JochiSt/OpenFlowMeter/images/aisler/EEPROM_jumper.PNG

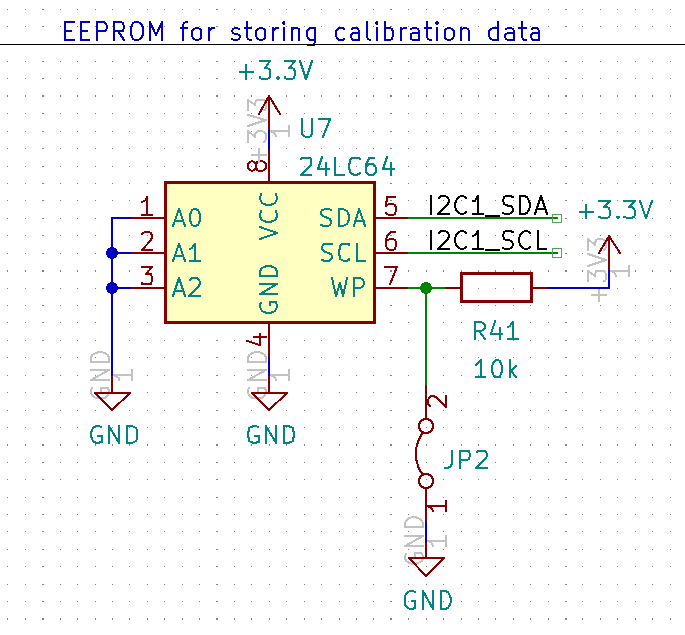
images/aisler/EEPROM_jumper.PNG
