JochiSt/OpenFlowMeter/simulations/CurrentSource/images/current_source_mod_v1_Iout_vs_Uin.PNG

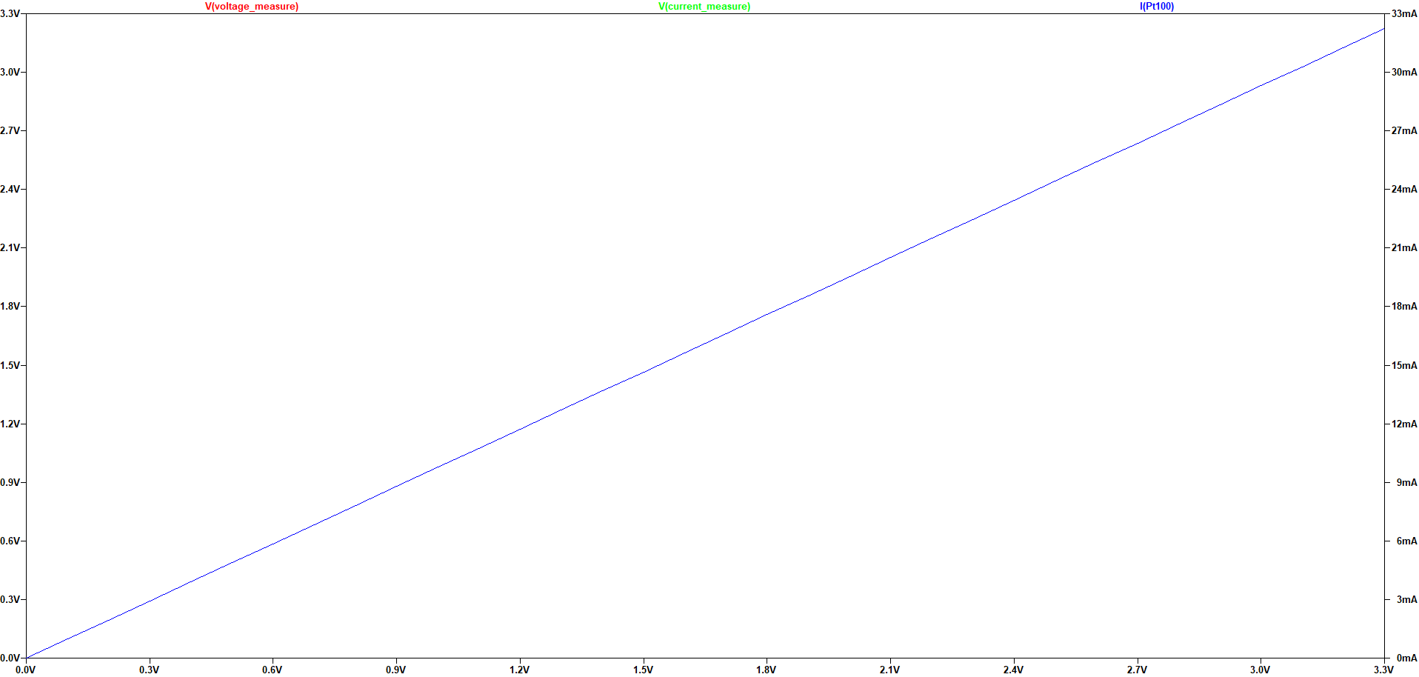
simulations/CurrentSource/images/current_source_mod_v1_Iout_vs_Uin.PNG
