JochiSt/OpenFlowMeter/software/measurements/3V3_zener_voltage_current.png

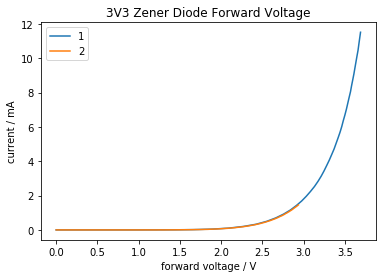
software/measurements/3V3_zener_voltage_current.png
