JochiSt/OpenFlowMeter/software/testing/calibration_20220307_190727_CH0_100.png

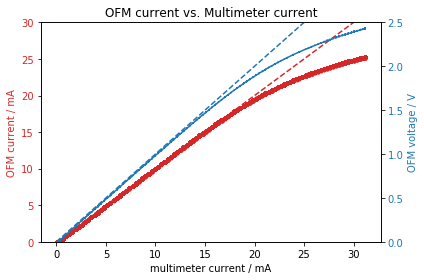
software/testing/calibration_20220307_190727_CH0_100.png
