JochiSt/OpenFlowMeter/simulations/AmplifierBias/SwitchableGainAmplifier.asc

C1: cap; 100n
R1: res; 47k
R2: res; 5k6
R5: res; 10k
R6: res; 100
U2: cd4066
U3: LT1491
V1: voltage; PULSE(0 3.3 1 10p 10p 1 2)
V2: voltage; PULSE(0 3.3 1 1 10p 0 1)
V3: voltage; 3.3
V4: voltage; PWL(0 0 2 0 2.1 0.5 4 0.5 4.1 1 6 1 6.1 1.5 8 1.5 8.1 2 10 2 10.1 2.5 12 2.5 12.1 3.3 14 3.3)
Named nets: 0, +3V3, AMPout, GainSwitch, AMPin, Vbias
.tran 14
