JochiSt/OpenFlowMeter/simulations/CurrentSource/current_source_mod_v1.asc

PT100: res; {R_PT100}
Q2: pnp; BC857C
R1: res; 47
R2: res; 100k
R3: res; 47k
R4: res; 47k
R5: res; 100
R6: res; 1k
R7: res; 220
R8: res; 22k
R9: res; 22k
R10: res; 10k
R11: res; 10k
R12: res; 10k
R13: res; 10k
R14: res; 10k
R15: res; 10k
R16: res; 8
R17: res; 8
R18: res; 8
R19: res; 8
U1: LT1490A
U2: LT1490A
U3: LT1490A
V1: voltage; 24
V3: voltage; 1.5
Named nets: +24V, 0, current_measure, voltage_measure, current_setpoint
.dc V3 0 3.3 0.1
.param R_PT100 100
R2 and R4 define current per input voltage
max. 3.3V
"protection" resistor
differential amplifier
measure voltage across R7
PT100 temperature sensor
.tran 1
.save V(voltage_measure) V(current_measure) I(Pt100)
.step param R_PT100 100 150 10
.measure Vmeas_avg avg V(voltage_measure)
.measure Imeas_avg avg V(current_measure)
.measure Ipt100_avg avg I(Pt100)
Simulate current vs PT100
Simulate current vs input voltage
