JochiSt/OpenFlowMeter/simulations/PWMFilter/pwm_filter_v1.asc

C1: cap; 100n
C2: cap; 100n
R1: res; {RR1}
R2: res; {RR2}
U1: LT1490A
V1: voltage; PULSE(0 3.3 0 1n 1n {Ton} {Tperiod}); AC 1
V2: voltage; 3.3
V3: voltage; {PWMoutVoltage}
Named nets: 0, 3V3, PWMin, Uout, OUTset
.param Ton={DutyCycle / FPWM}
.param Tperiod={ 1 / FPWM }
;.tran 0 20ms 0
* calculate PWM frequency
* MasterClock Frequency = 54MHz
.param FCLK={54Meg}
* ARR = 16bit = 65536
;.param ARR = {65536}
* ARR = 10bit = 1024
* ARR = 12bit = 4096
.param ARR = {4096}
* Prescaler
.param PSC ={0}
 * calculate PWM frequency
.param FPWM = {FCLK / ( (ARR + 1) * (PSC + 1) )}
 * calculate DutyCycle
.param DutyCycle = { CCR / ARR }
* relative PWM value
.param relPWM=0.3
* calculate timer setting
.param CCR = { ARR * relPWM }
* analog equivalent voltage
.param PWMoutVoltage = {3.3 * relPWM}
PWM setting
STM32 internal calculations
* See SPICE Error Log for result
.meas tran T1 find time when V(pwmin)=0 rise 1
.meas tran T2 find time when V(pwmin)=0 rise 2
.meas tran  Frequency param 1/(T2-T1)
.meas Cfreq PARAM FPWM
PWM output generation
Measure Frequency
.ac dec 100 10 1k
.meas gmax max(mag(V(uout)))
.meas AC f FIND frequency when mag(V(uout))=gmax/sqrt(2)
Measure -3B point (see log)
.step param RR2 list 1k 4k7 10k
.step param RR1 list 1k 4k7 10k
