JochiSt/OpenFlowMeter/simulations/GainSwitchAmplifier/SwitchableGainAmplifier.asc

C1: cap; 100n
M1: nmos; BSS123
R1: res; 10k
R2: res; 10k
R3: res; 10k
R4: res; 10
R5: res; 10k
R6: res; 100
U1: LT1492
V1: voltage; PULSE(0 3.3 0.5 10n 10n 0.5 1)
V2: voltage; PULSE(0 3.3 0 10 10 0 20)
V3: voltage; 3.3
Named nets: 0, +3V3, AMPout, GainSwitch, AMPin
.tran 10
