JochiSt/OpenFlowMeter/simulations/ZenerDiode/ADC_InputProtection.asc

D1: zener; 3V3zener
R1: res; 1k
R2: res; 50k
V1: voltage; 0
Named nets: 0, ADCInput, VIN
4V7 Zener
.dc V1 0 4 0.01
.model 3V3zener ako:  1N750 bv=3.3
use existing model and overwrite the breakdown voltage
