JochiSt/OpenFlowMeter/firmware/Inc/adc.h

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
/* Define to prevent recursive inclusion -------------------------------------*/
#ifndef __ADC_H__
#define __ADC_H__

#ifdef __cplusplus
extern "C" {
#endif

/* Includes ------------------------------------------------------------------*/
#include "main.h"

extern ADC_HandleTypeDef hadc1;

/* USER CODE BEGIN Private defines */

#define ADC_BUFLEN 6                            // 4 external inputs + T + Uint
extern uint32_t adcBuf[ADC_BUFLEN];             // store the ADC samples
extern uint16_t avr_adcBuf_GAIN_0[ADC_BUFLEN];  // average the ADC samples with
                                                // moving average
extern uint16_t avr_adcBuf_GAIN_1[ADC_BUFLEN];
extern uint16_t adc_result_cnt;  ///< count the received ADC results

extern uint8_t adc_result_received;

extern uint16_t* avr_current[2][2];
extern uint16_t* avr_voltage[2][2];

/* USER CODE END Private defines */

void MX_ADC1_Init(void);

#ifdef __cplusplus
}
#endif

#endif /* __ADC_H__ */
