JochiSt/OpenFlowMeter/firmware/Inc/i2c_utils.h

#ifndef __I2C_UTILS_H__
#define __I2C_UTILS_H__

#ifdef __cplusplus
extern "C" {
#endif

#include "stm32f1xx_hal.h"

uint8_t write8_EEPROM(I2C_HandleTypeDef* i2cHandle, uint8_t EEPROM_addr, uint8_t addr, uint8_t value);
uint8_t read8_EEPROM(I2C_HandleTypeDef* i2cHandle, uint8_t EEPROM_addr, uint8_t addr);

void i2c_init_TMP100(I2C_HandleTypeDef* i2cHandle, uint8_t TMP100_addr);
uint16_t i2c_read_TMP100(I2C_HandleTypeDef* i2cHandle, uint8_t TMP100_addr);

#ifdef __cplusplus
}
#endif

#endif /* __I2C_UTILS_H__ */
