JochiSt/OpenFlowMeter/firmware/Src/utils.c

#include "utils.h"

uint8_t upper(uint16_t val){
	return (val >> 8) & 0xFF;
};
uint8_t lower(uint16_t val){
	return (val & 0xFF);
};

/**
 * convert the resistance of a PT100 into its temperature
 * @param resistance PT100 resistance
 * @return temperature derived from the given resistance
 */
float convertPT100_R2T(float resistance){
    const float A = 3.9083e-3;
    //const float B = -5.775e-7;
    const float R0 = 100;
    return (resistance - R0)/(R0 * A);
}
